ChewbaccaBox/Williams-ROM-Board-Ribbon-Cable-Adapter/Kicad Source/Defenderthing.sch

## KiCad design Kicad Source/Defenderthing.sch (2022-06-01)

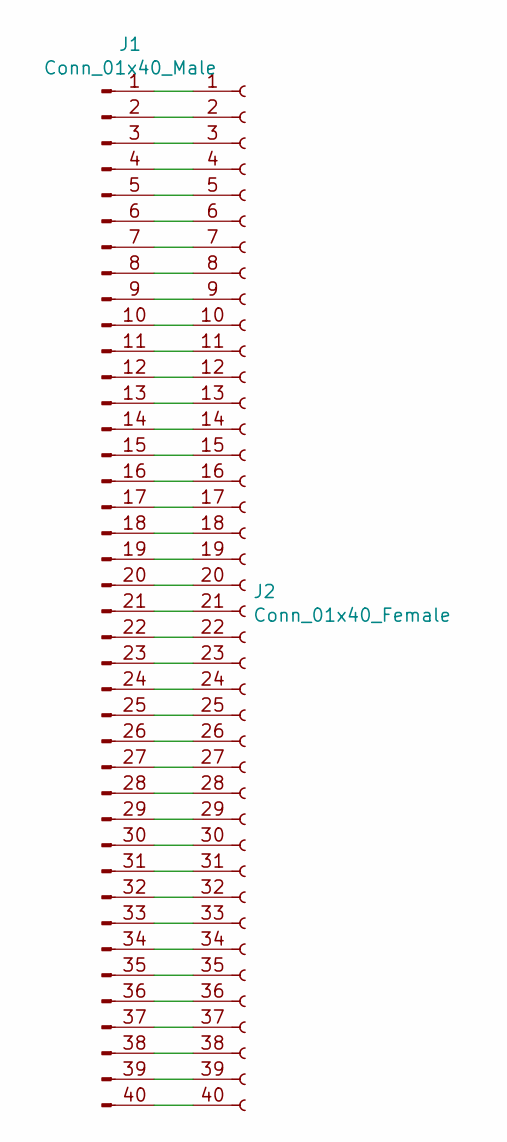
[picture p8: schematic Defenderthing.sch]

Parts:
J1: Conn_01x40_Male; defe
J2: Conn_01x40_Female; PinHeader_2x20_P2.54mm_Vertical

Connections:
unnamed: J1.1, J2.1
unnamed: J1.2, J2.2
unnamed: J1.3, J2.3
unnamed: J1.4, J2.4
unnamed: J1.5, J2.5
unnamed: J1.6, J2.6
unnamed: J1.7, J2.7
unnamed: J1.8, J2.8
unnamed: J1.9, J2.9
unnamed: J1.10, J2.10
unnamed: J1.11, J2.11
unnamed: J1.12, J2.12
unnamed: J1.13, J2.13
unnamed: J1.14, J2.14
unnamed: J1.15, J2.15
unnamed: J1.16, J2.16
unnamed: J1.17, J2.17
unnamed: J1.18, J2.18
unnamed: J1.19, J2.19
unnamed: J1.20, J2.20
unnamed: J1.21, J2.21
unnamed: J1.22, J2.22
unnamed: J1.23, J2.23
unnamed: J1.24, J2.24
unnamed: J1.25, J2.25
unnamed: J1.26, J2.26
unnamed: J1.27, J2.27
unnamed: J1.28, J2.28
unnamed: J1.29, J2.29
unnamed: J1.30, J2.30
unnamed: J1.31, J2.31
unnamed: J1.32, J2.32
unnamed: J1.33, J2.33
unnamed: J1.34, J2.34
unnamed: J1.35, J2.35
unnamed: J1.36, J2.36
unnamed: J1.37, J2.37
unnamed: J1.38, J2.38
unnamed: J1.39, J2.39
unnamed: J1.40, J2.40
